jonesandjay123/3dmakerpro-fox-case/reference/photos/PXL_20260927_172336048.jpg

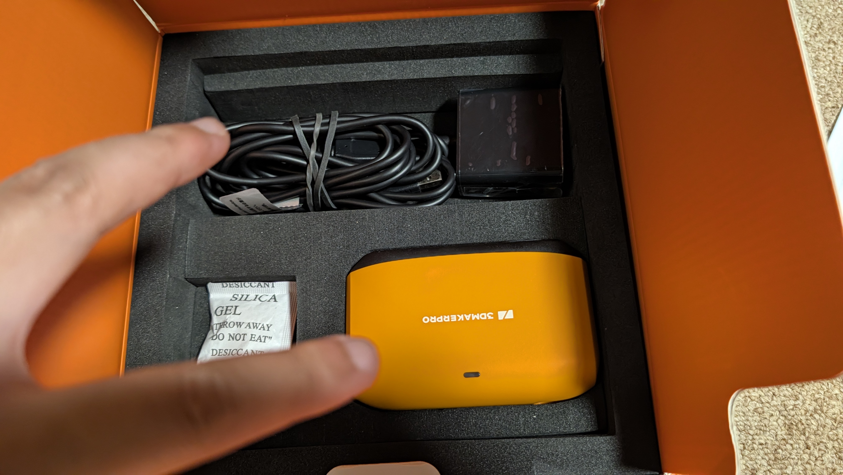
reference/photos/PXL_20260927_172336048.jpg
