jonesandjay123/3dmakerpro-fox-case/reference/photos/PXL_20260927_174137416.jpg

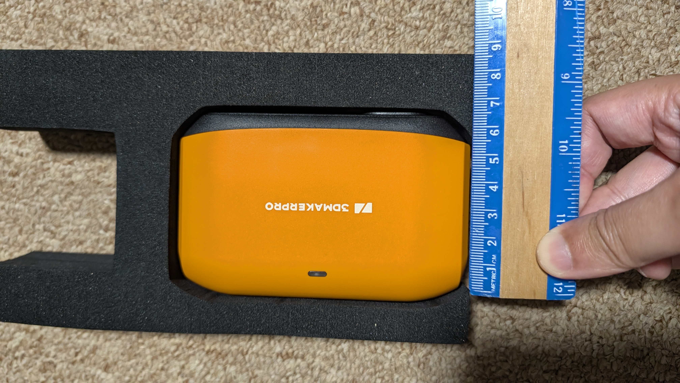
reference/photos/PXL_20260927_174137416.jpg
