jonesandjay123/3dmakerpro-fox-case/reference/photos/PXL_20260927_174550251.MACRO_FOCUS.jpg

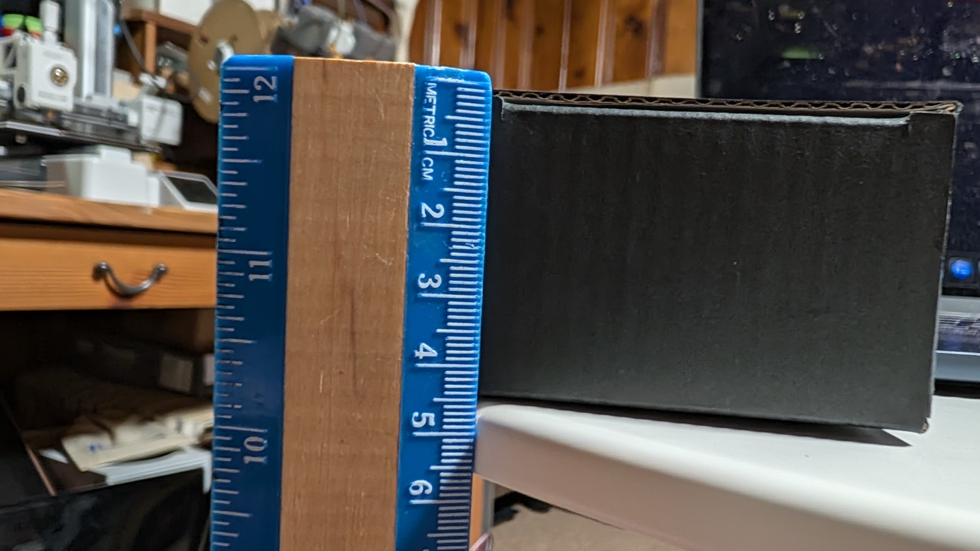
reference/photos/PXL_20260927_174550251.MACRO_FOCUS.jpg
