jonesandjay123/3dmakerpro-fox-case/renders/02_open_case_fox_inside.png

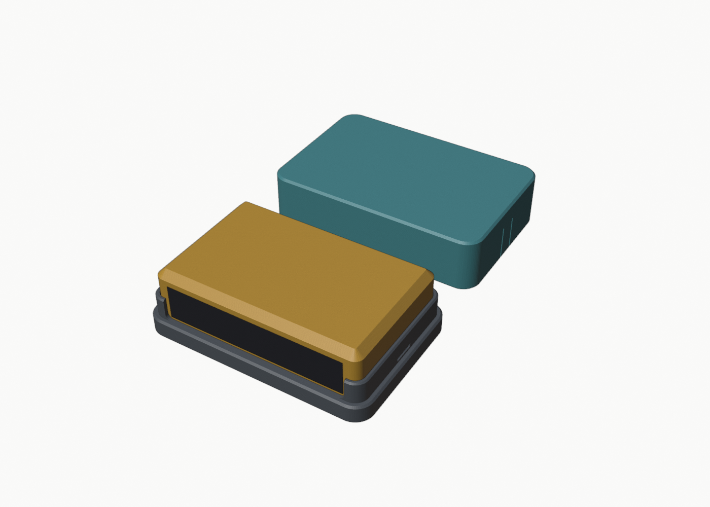
renders/02_open_case_fox_inside.png
