jonesandjay123/3dmakerpro-fox-case/renders/05_section_clearance.png

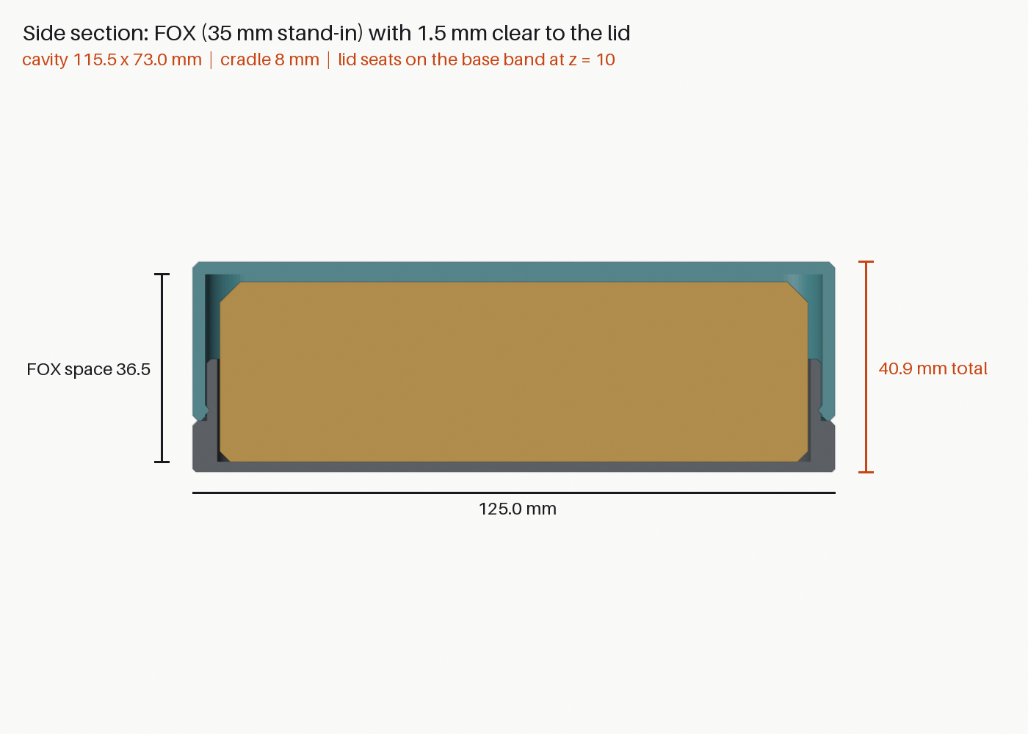
renders/05_section_clearance.png
