jonesandjay123/3dmakerpro-fox-case/renders/05_section_stack_height.png

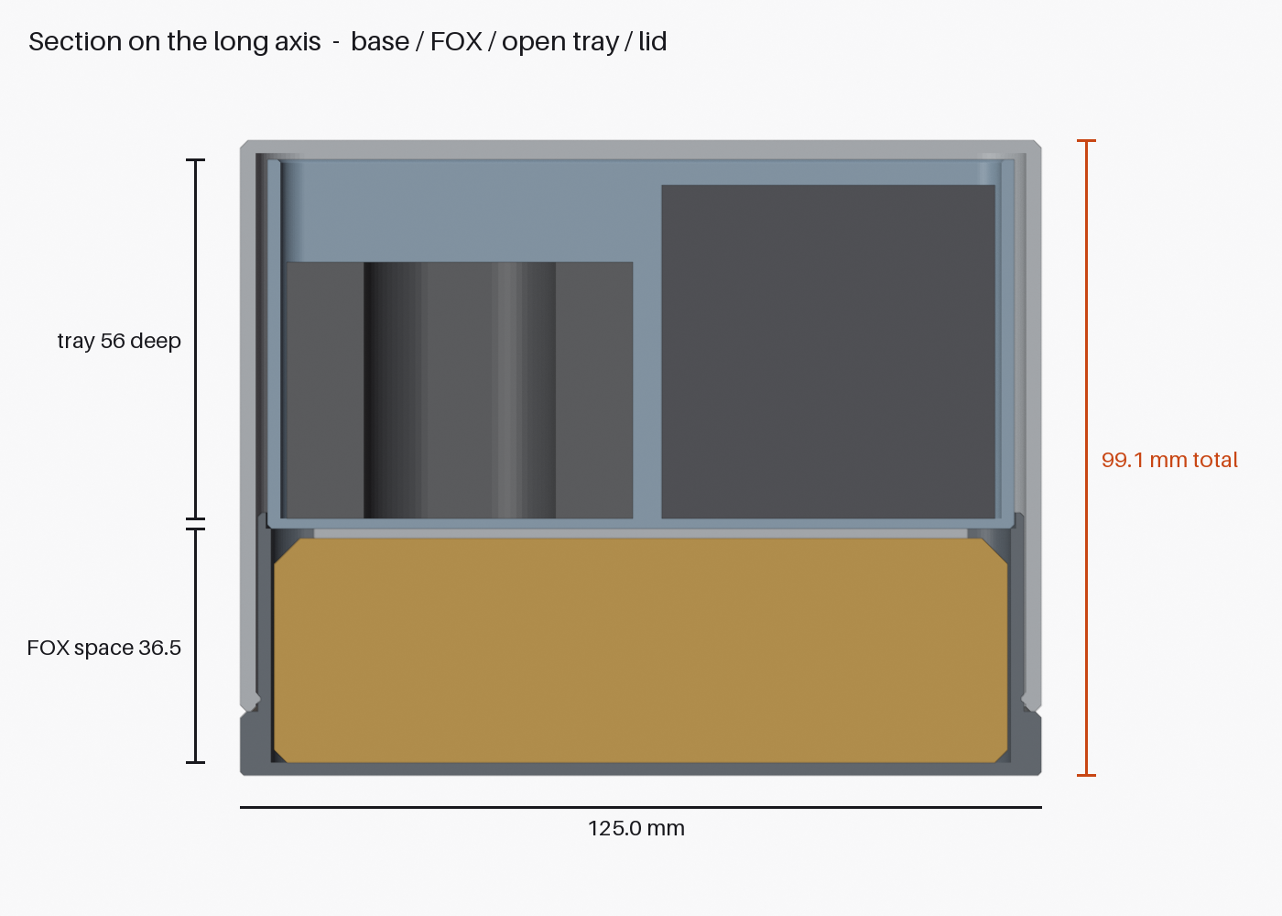
renders/05_section_stack_height.png
