jonesandjay123/3dmakerpro-fox-case/renders/05b_section_3q.png

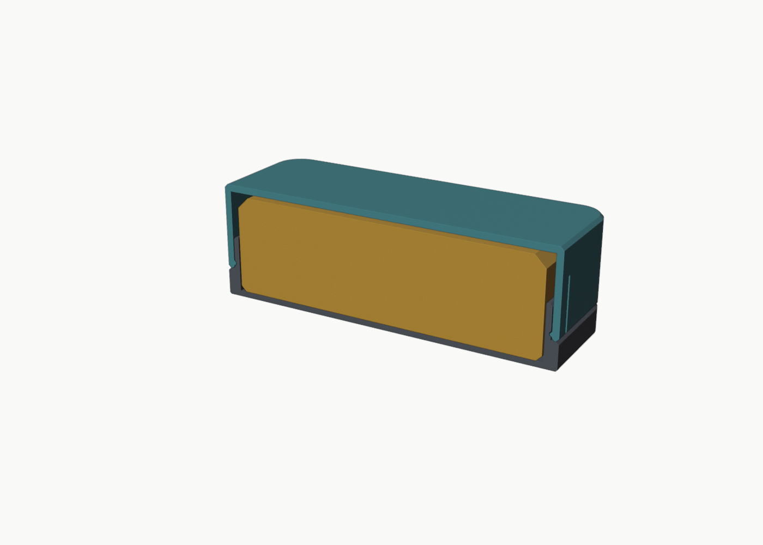
renders/05b_section_3q.png
