jonesandjay123/3dmakerpro-fox-case/renders/05c_cross_section_width.png

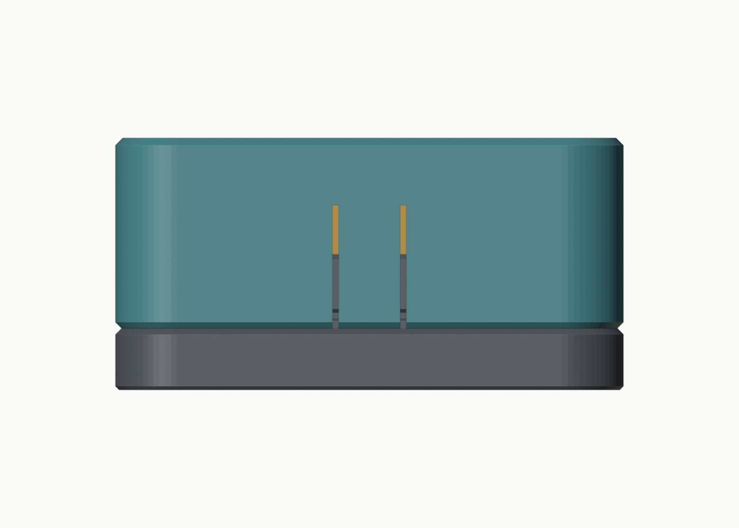
renders/05c_cross_section_width.png
