jonesandjay123/3dmakerpro-fox-case/renders/07_snap_tab_section.png

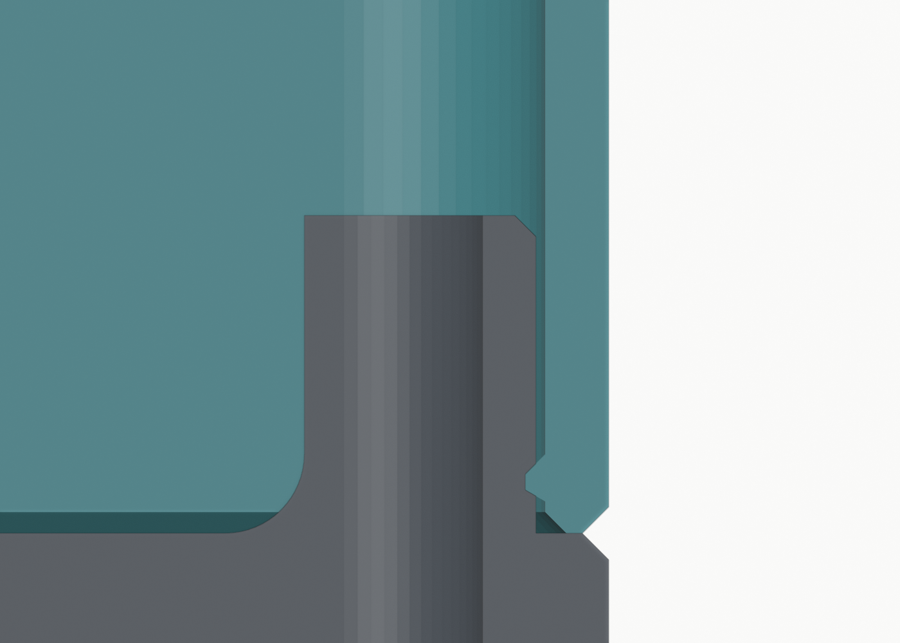
renders/07_snap_tab_section.png
