jonesandjay123/3dmakerpro-fox-case/renders/08_one_plate_A1mini.png

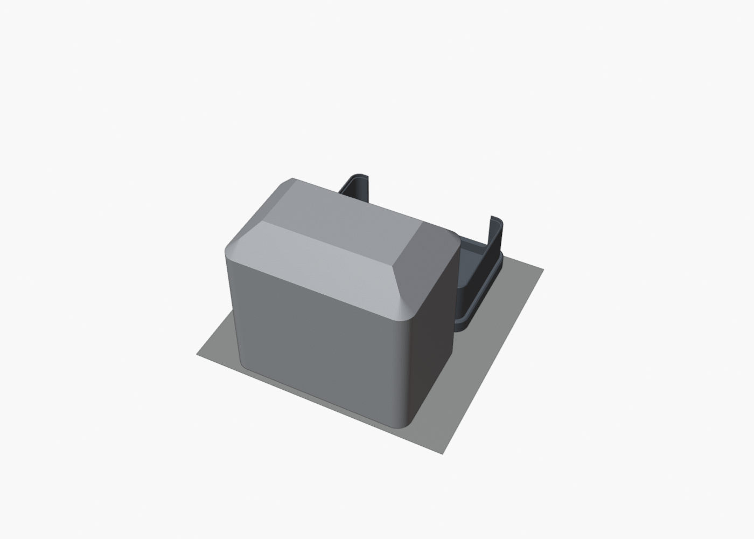
renders/08_one_plate_A1mini.png
