jonesandjay123/3dmakerpro-fox-case/renders/09_print_progress_sheet.png

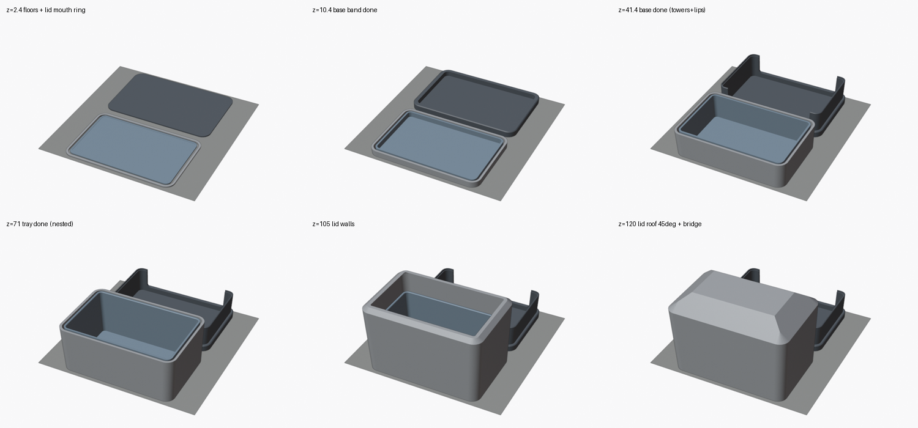
renders/09_print_progress_sheet.png
