jonesandjay123/3dmakerpro-fox-case/reference/fit_test_v2_ring/ring_sensor_face.jpg

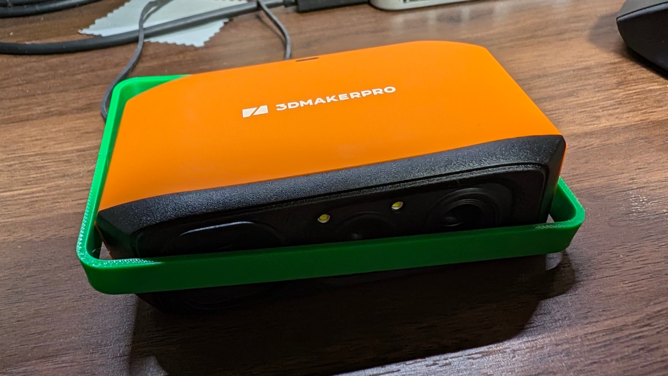
reference/fit_test_v2_ring/ring_sensor_face.jpg
