jonesandjay123/3dmakerpro-fox-case/reference/fit_test_v2_ring/ring_top_view.jpg

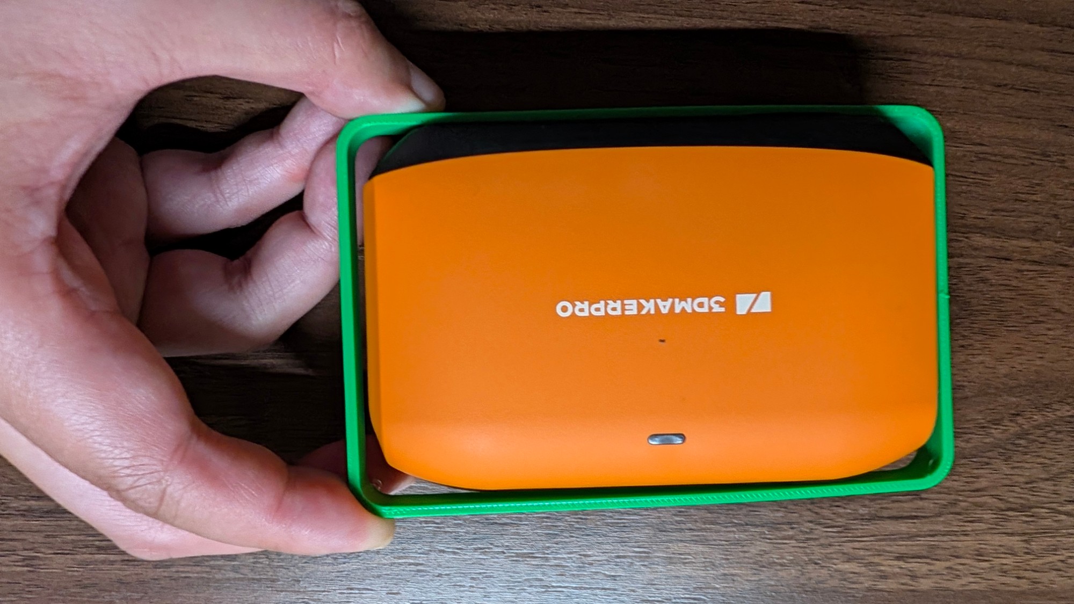
reference/fit_test_v2_ring/ring_top_view.jpg
