jonesandjay123/3dmakerpro-fox-case/reference/fit_test_v2_ring/ring_width_ruler.jpg

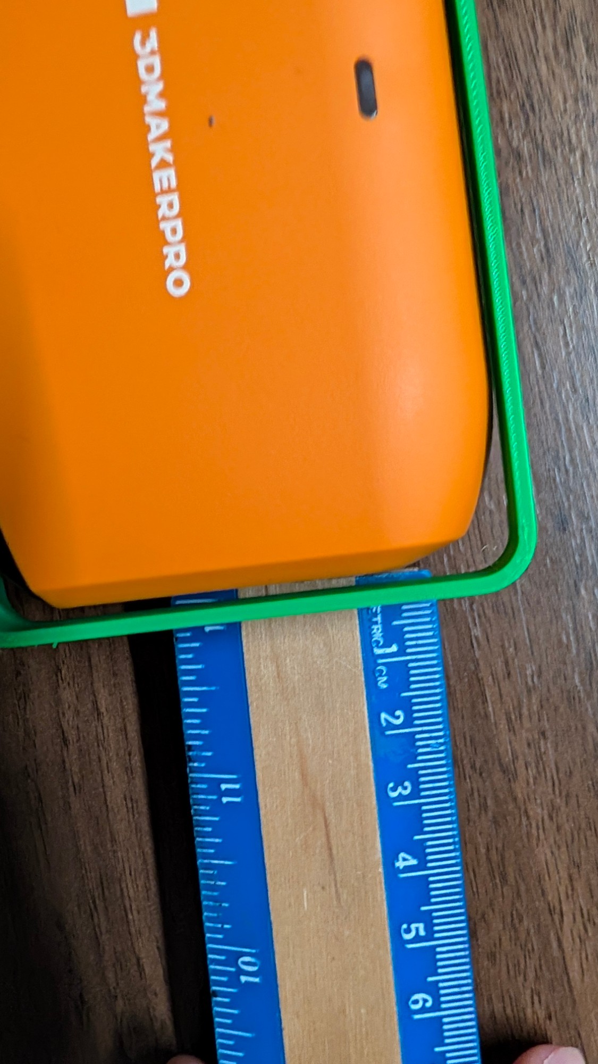
reference/fit_test_v2_ring/ring_width_ruler.jpg
